TheMarshall1/Senior-Design-2/DataSheet/3D-Model/top.png

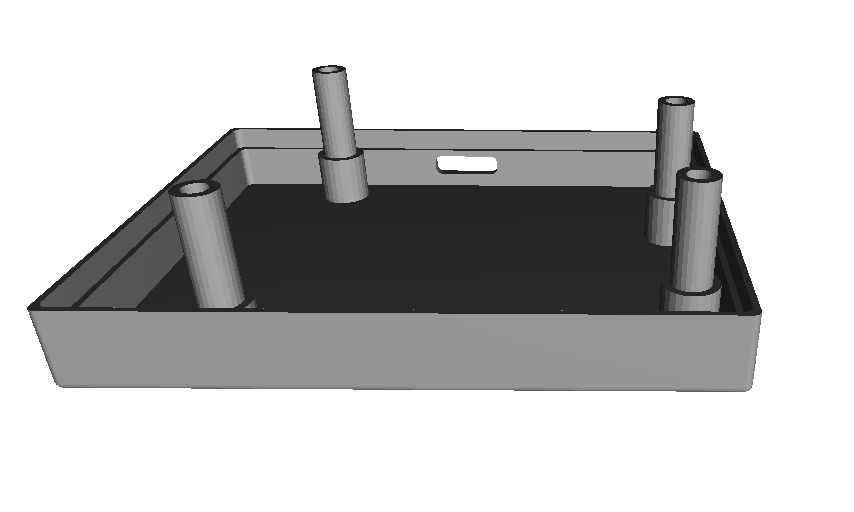
DataSheet/3D-Model/top.png
