TheMarshall1/Senior-Design-2/DataSheet/3D-Model/whole.png

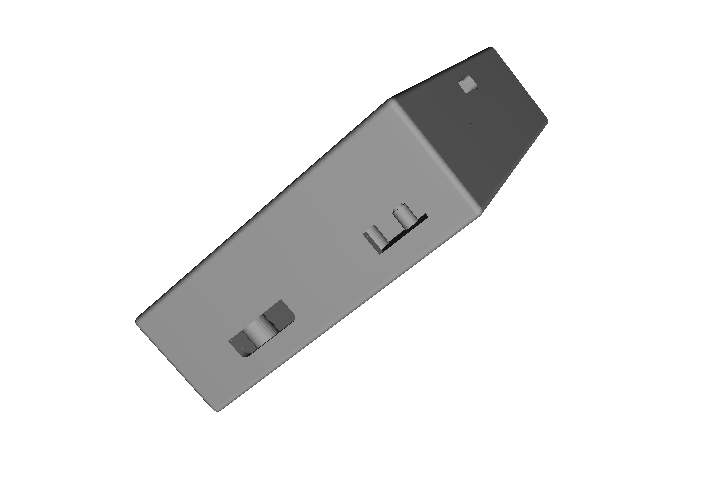
DataSheet/3D-Model/whole.png
