TheMarshall1/Senior-Design-2/DataSheet/Bed Board Drawing.JPG

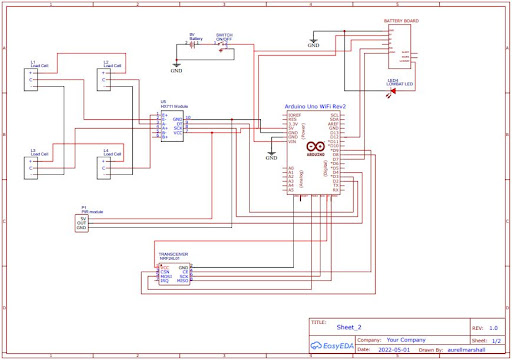
DataSheet/Bed Board Drawing.JPG
