TheMarshall1/Senior-Design-2/DataSheet/Door Board Drawing.png

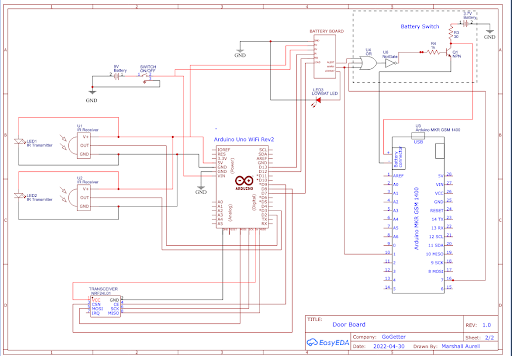
DataSheet/Door Board Drawing.png
