TheMarshall1/Senior-Design-2/DataSheet/IR.PNG

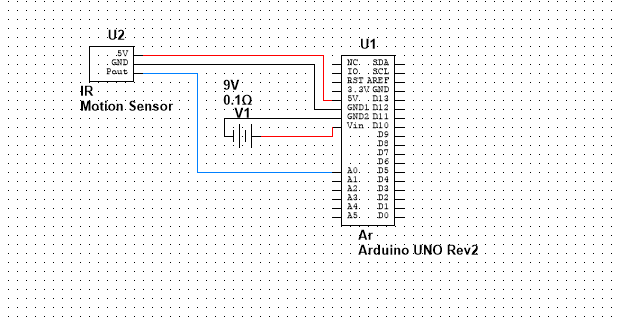
DataSheet/IR.PNG
