TheMarshall1/Senior-Design-2/DataSheet/PCB-Data/PCB-3d.PNG

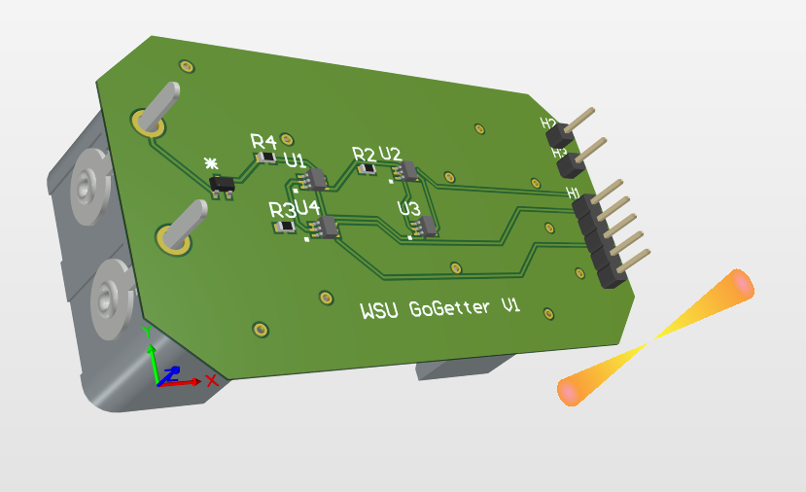
DataSheet/PCB-Data/PCB-3d.PNG
