TheMarshall1/Senior-Design-2/Code/client.ino

#include <SPI.h>
#include <WiFiNINA.h>

char ssid[] = "Jupiterbean";          //  your network SSID (name)
char pass[] = "Ma351968";   // your network password

int status = WL_IDLE_STATUS;
char servername[]="192.168.1.11";  // remote server we will connect to

WiFiClient client;

void setup() {
  Serial.begin(9600);
  Serial.println("Attempting to connect to WPA network...");
  Serial.print("SSID: ");
  Serial.println(ssid);

  status = WiFi.begin(ssid, pass);
  if ( status != WL_CONNECTED) {
    Serial.println("Couldn't get a wifi connection");
    // don't do anything else:
    while(true);
  }
  else {
    Serial.println("Connected to wifi");
    Serial.println("\nStarting connection...");
    // if you get a connection, report back via serial:
    if (client.connect(servername, 80)) {
      Serial.println("connected");
      // Make a HTTP request:
      client.println("GET /search?q=arduino HTTP/1.0");
      client.println();
    }
  }
}

void loop() {

}
